ssmiao/Intel-I210-network-card/PCBV3.0/inteli210AT_3D.jpg

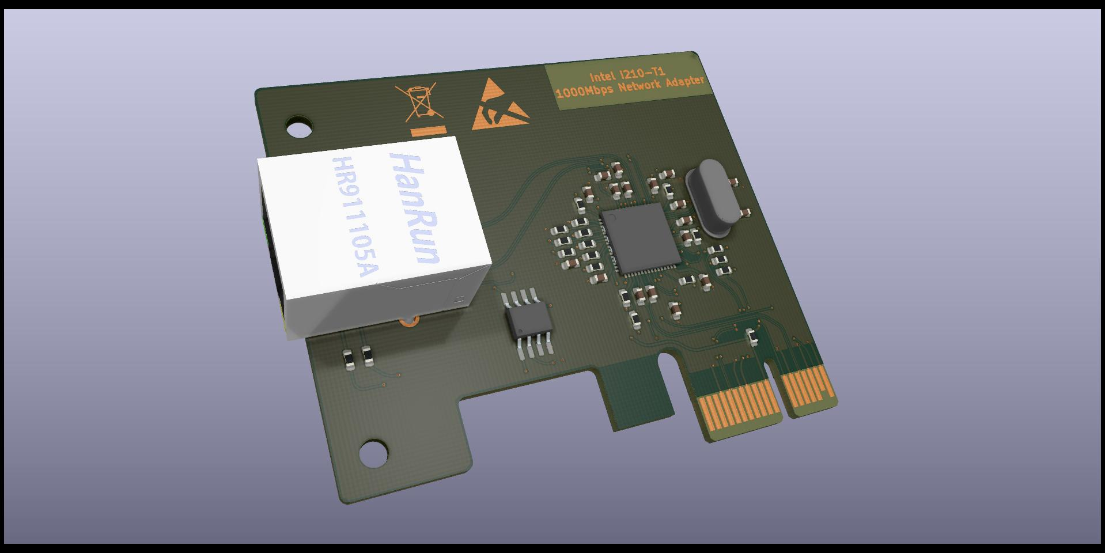
PCBV3.0/inteli210AT_3D.jpg
